rosshibb/OTWG-Lantern/OTGW_Spout_Wire_Pinch.STL

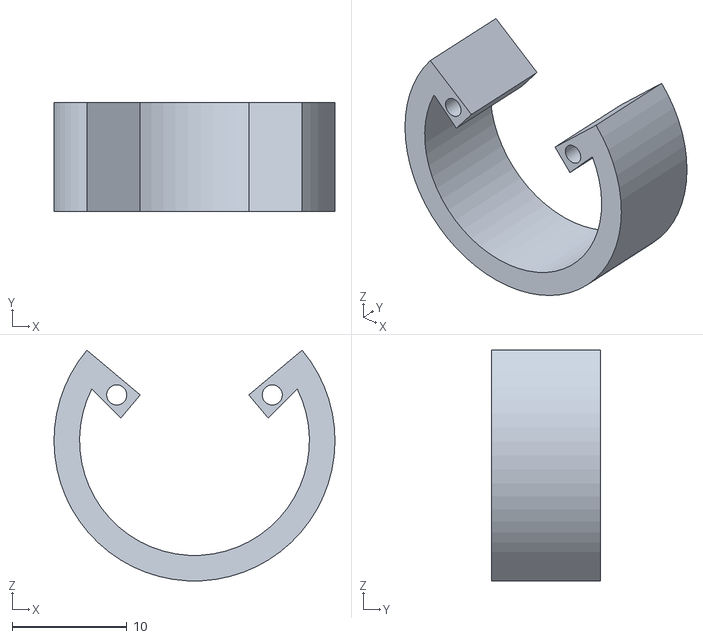
[picture p20: CAD file, 2025-12-09]
OTGW_Spout_Wire_Pinch.STL
24.4 x 9.50 x 20.1
