rosshibb/OTWG-Lantern/OTGW_Spout_Base.STL

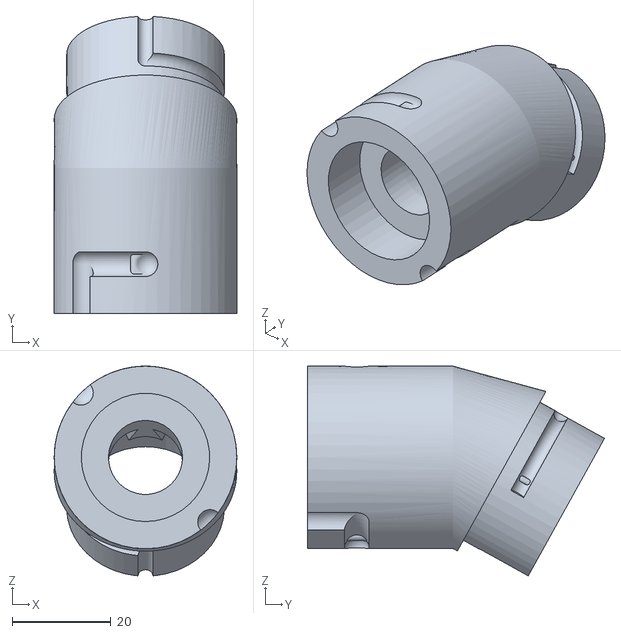
[picture p21: CAD file, 2025-12-09]
OTGW_Spout_Base.STL
37.0 x 60.2 x 42.5
